wszeto9/wifi-LED-poi/images/poi_PCB_bottom_decal.jpg

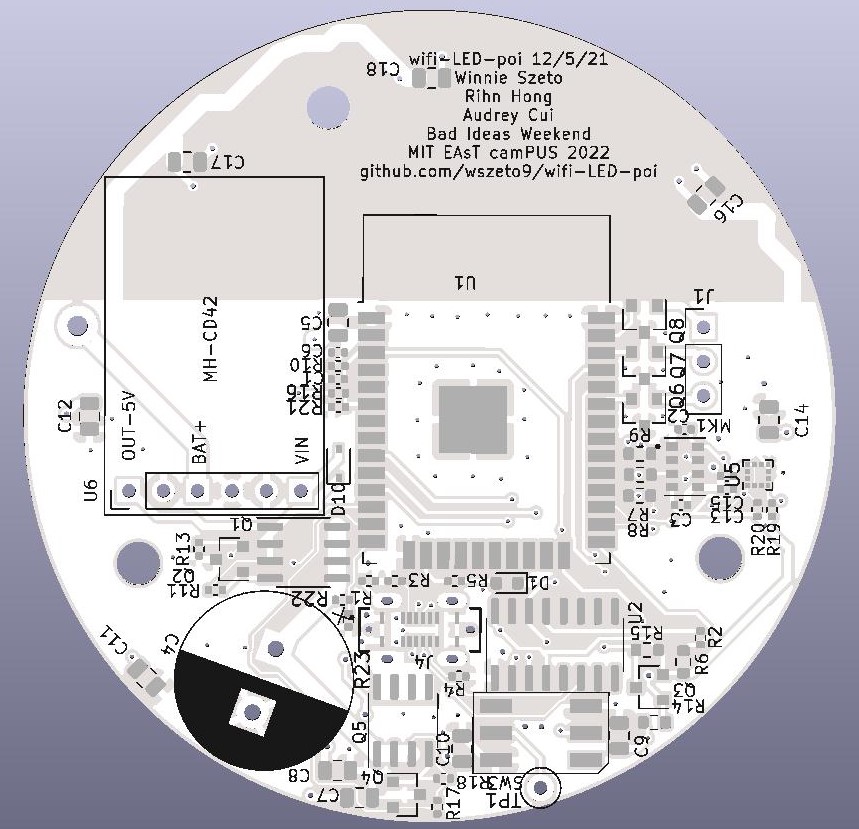
images/poi_PCB_bottom_decal.jpg
