wszeto9/wifi-LED-poi/images/poi_PCB_top_decal.jpg

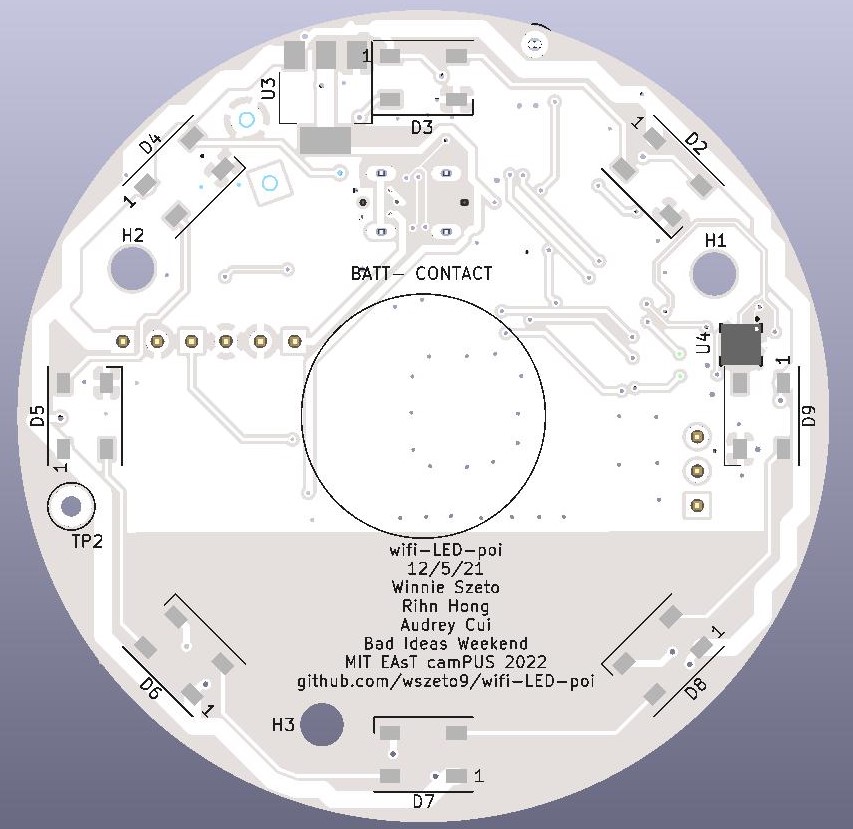
images/poi_PCB_top_decal.jpg
