wszeto9/wifi-LED-poi/manufacturing/3D print/PCB_spacer.3mf

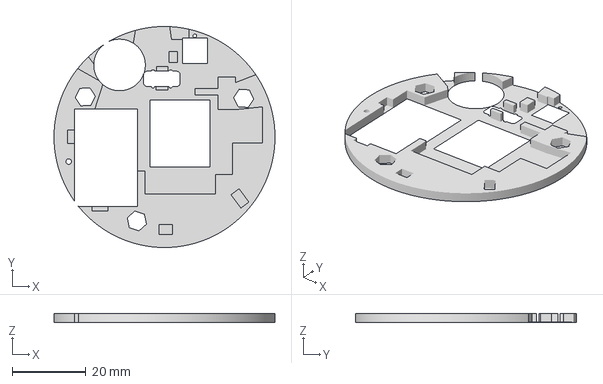
[picture p41: CAD file, 2021-12-11]
manufacturing/3D print/PCB_spacer.3mf
60.0 x 60.0 x 2.40 mm
