wszeto9/wifi-LED-poi/manufacturing/3D print/outer_cover.3mf

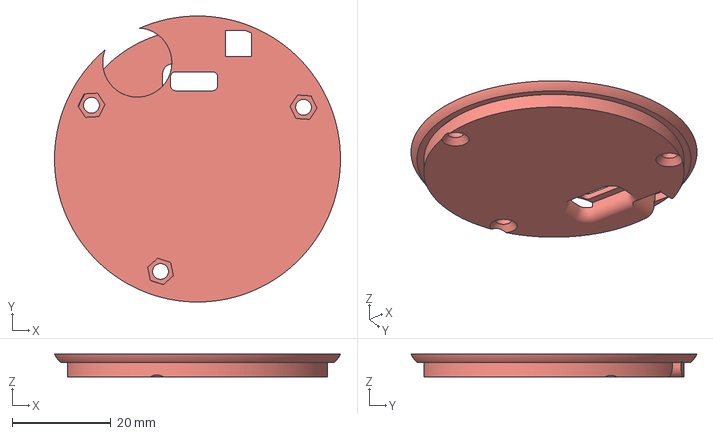
[picture p42: CAD file, 2021-12-11]
manufacturing/3D print/outer_cover.3mf
58.0 x 58.0 x 4.65 mm
