wszeto9/wifi-LED-poi/manufacturing/3D print/bottom_batt_support.3mf

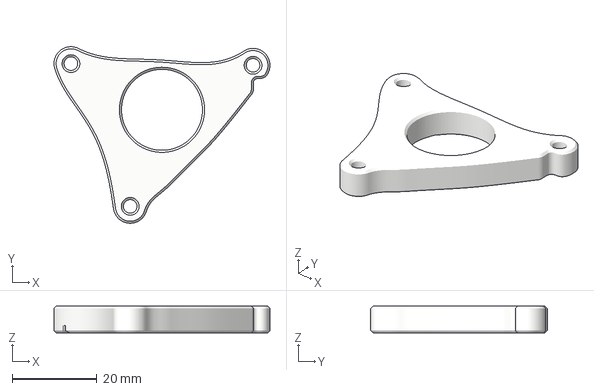
[picture p43: CAD file, 2021-12-11]
manufacturing/3D print/bottom_batt_support.3mf
51.0 x 41.7 x 6.28 mm
