wszeto9/wifi-LED-poi/manufacturing/Technical documents/MoldAssemblyVideo.gif

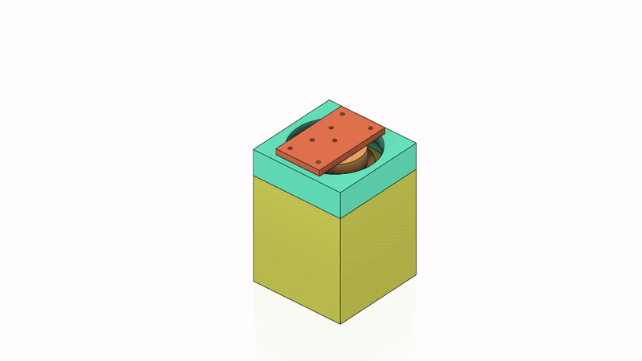
manufacturing/Technical documents/MoldAssemblyVideo.gif
